TheReincarnator/leguino/docs/ideas/Robotik-für-Kinder.jpg

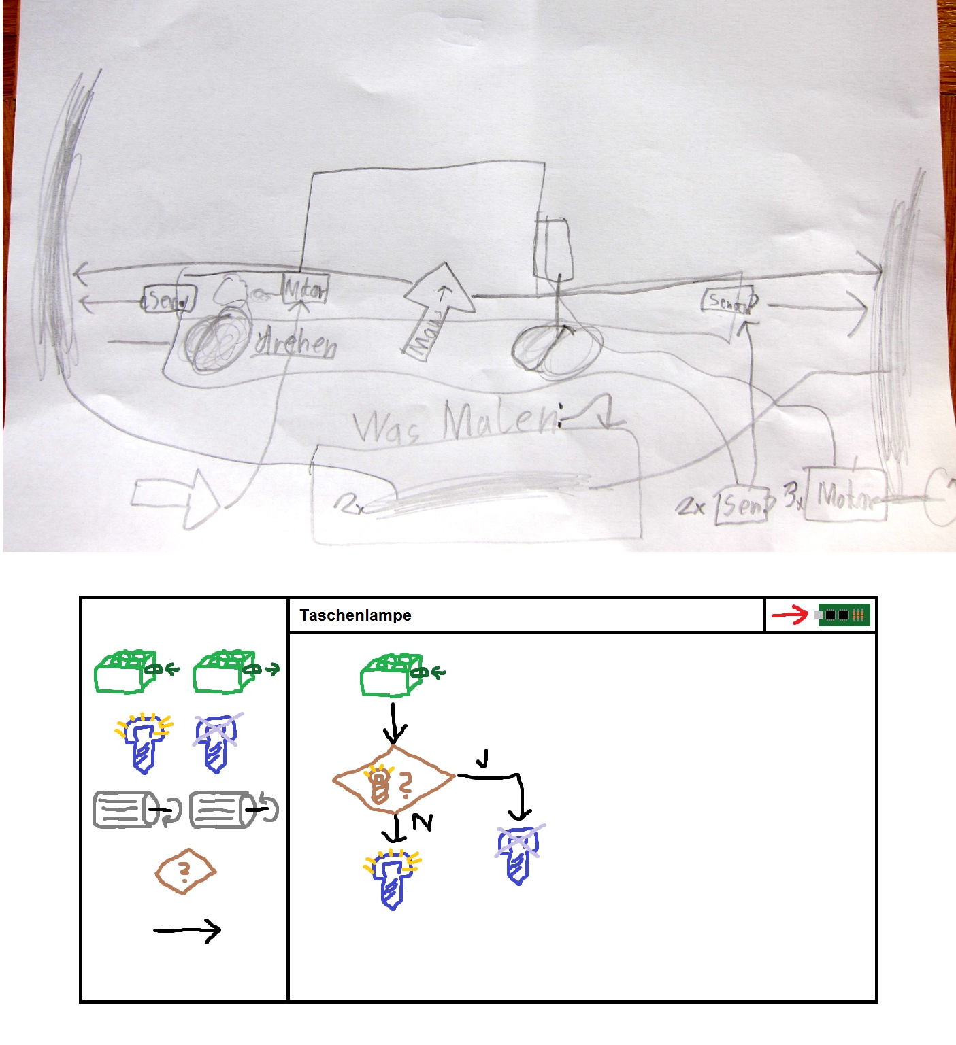
docs/ideas/Robotik-für-Kinder.jpg
