TheReincarnator/leguino/docs/photos/Leguino-Hardware-1.jpg

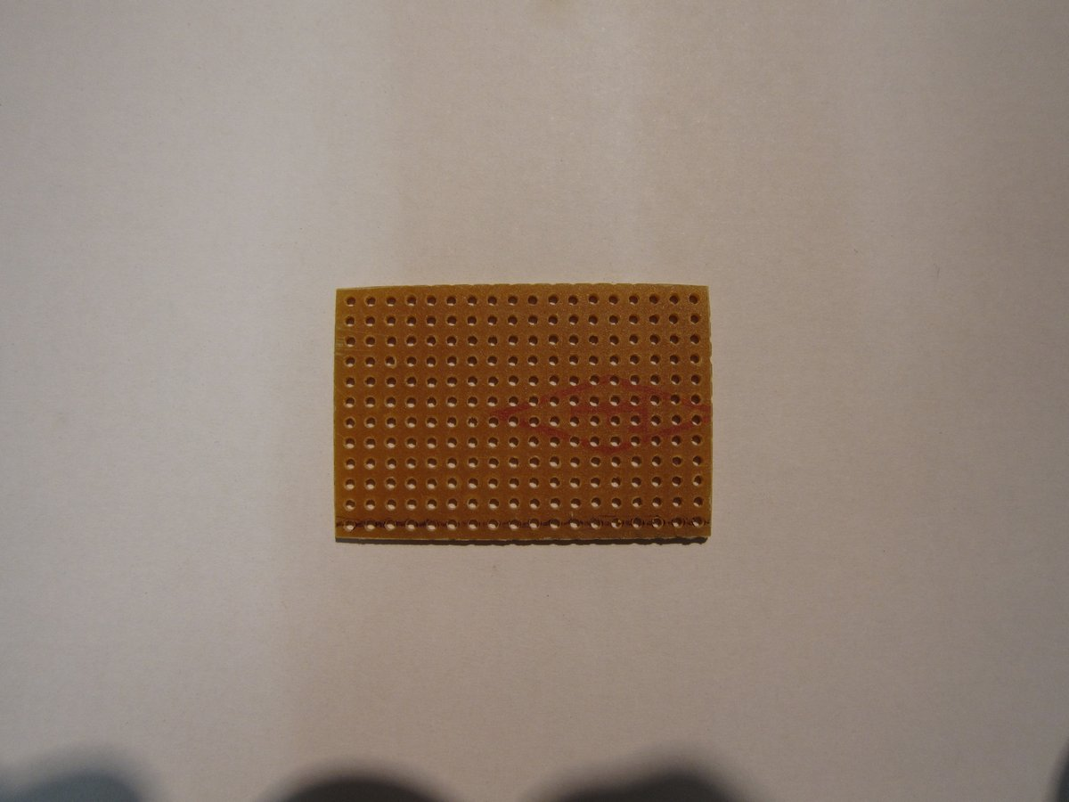
docs/photos/Leguino-Hardware-1.jpg
