TheReincarnator/leguino/docs/photos/Leguino-Hardware-3.jpg

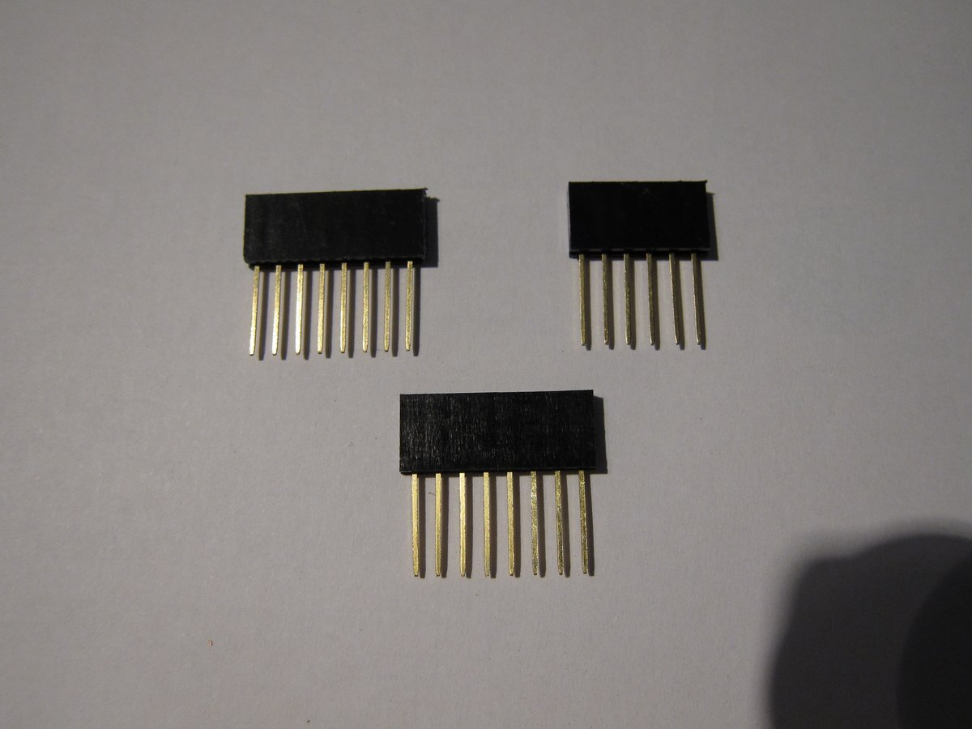
docs/photos/Leguino-Hardware-3.jpg
