TheReincarnator/leguino/docs/photos/Leguino-Hardware-4.jpg

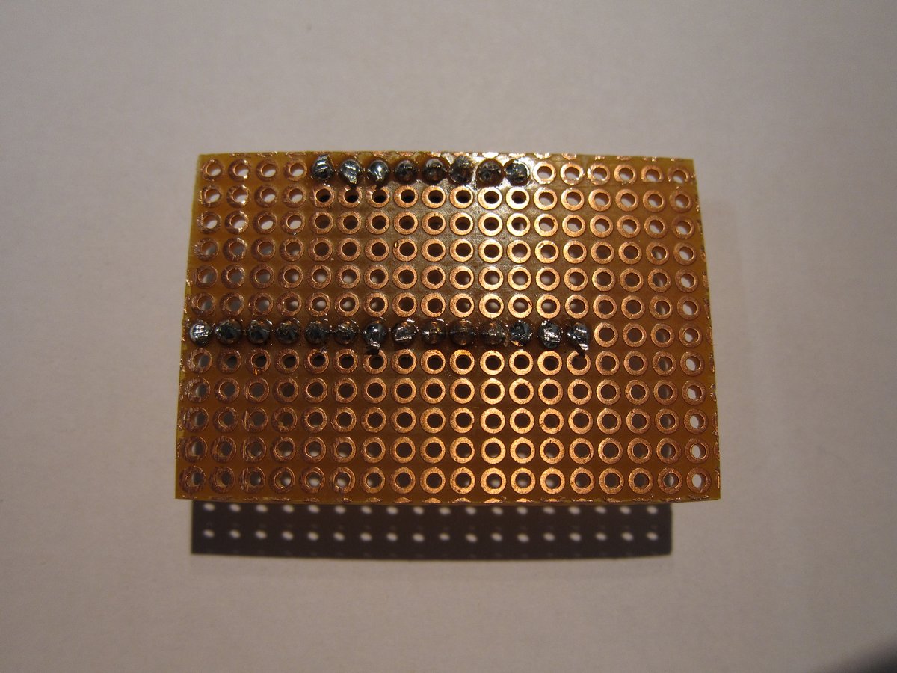
docs/photos/Leguino-Hardware-4.jpg
