TheReincarnator/leguino/docs/photos/Leguino-Hardware-5.jpg

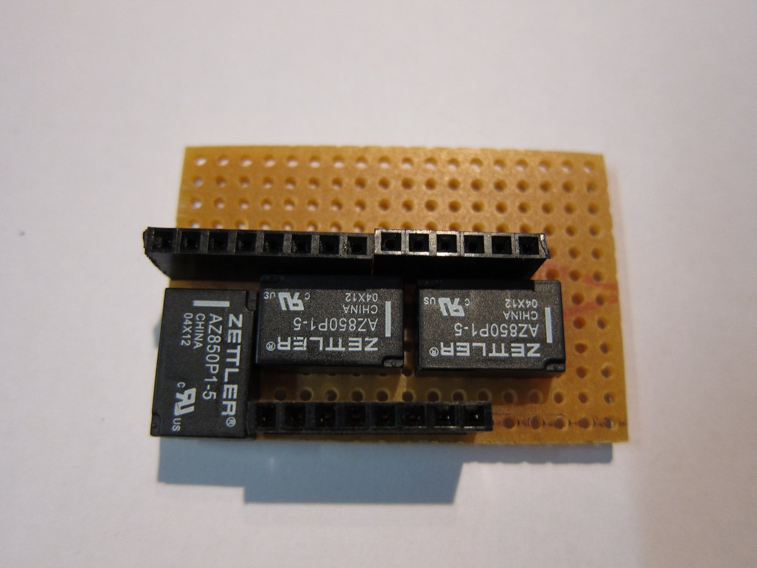
docs/photos/Leguino-Hardware-5.jpg
