TheReincarnator/leguino/docs/photos/Leguino-Hardware-6.jpg

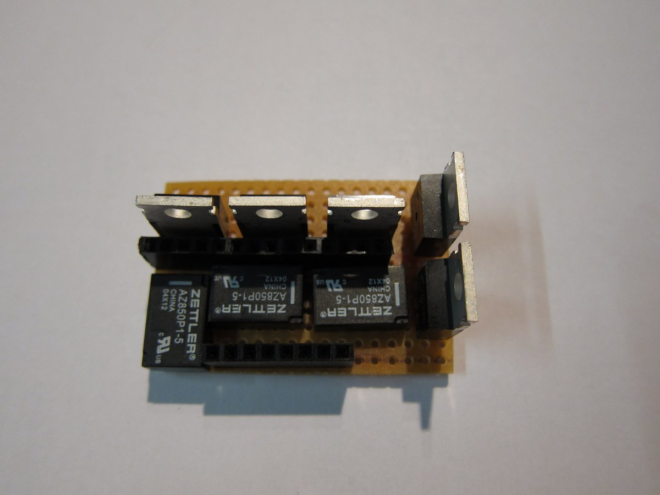
docs/photos/Leguino-Hardware-6.jpg
