TheReincarnator/leguino/docs/photos/Leguino-Hardware-7.jpg

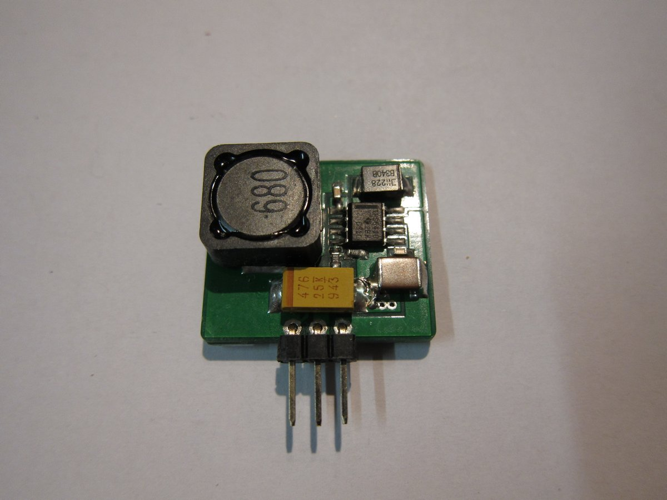
docs/photos/Leguino-Hardware-7.jpg
