TheReincarnator/leguino/docs/photos/Leguino-Hardware-8.jpg

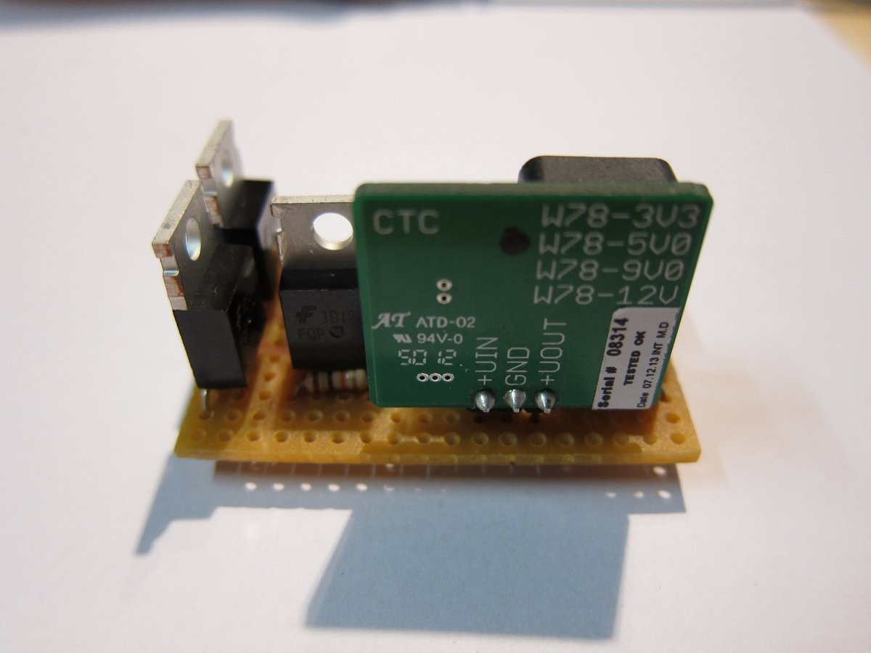
docs/photos/Leguino-Hardware-8.jpg
