TheReincarnator/leguino/docs/photos/Leguino-Hardware-9.jpg

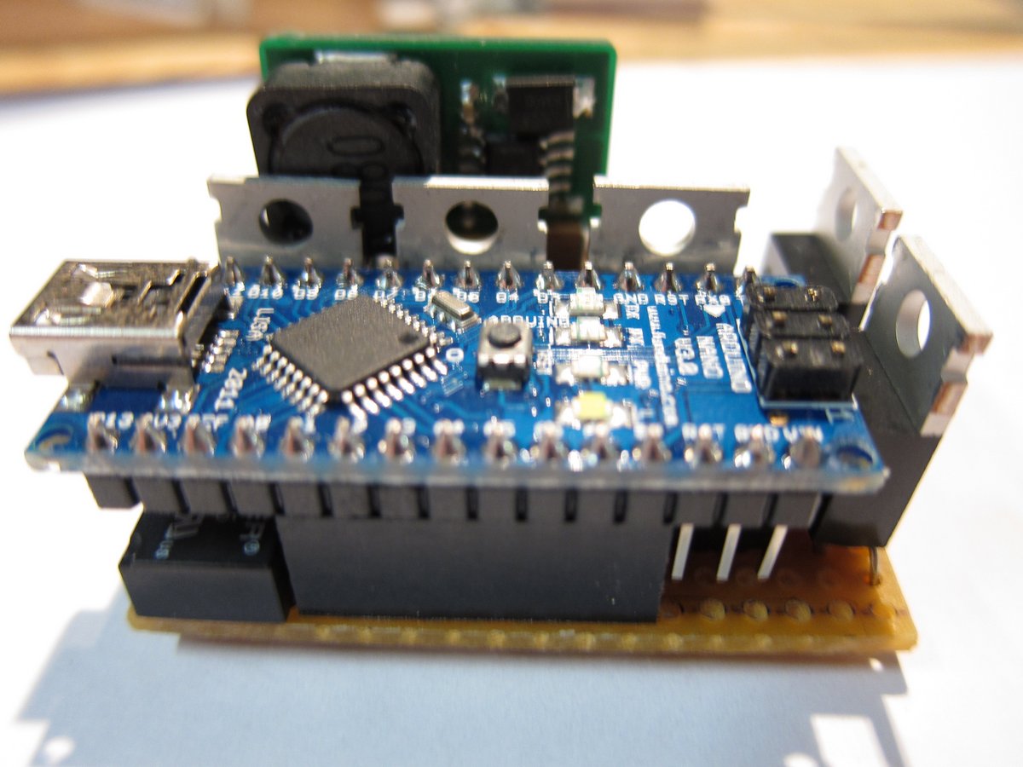
docs/photos/Leguino-Hardware-9.jpg
