TheReincarnator/leguino/docs/photos/Leguino-Hardware-10.jpg

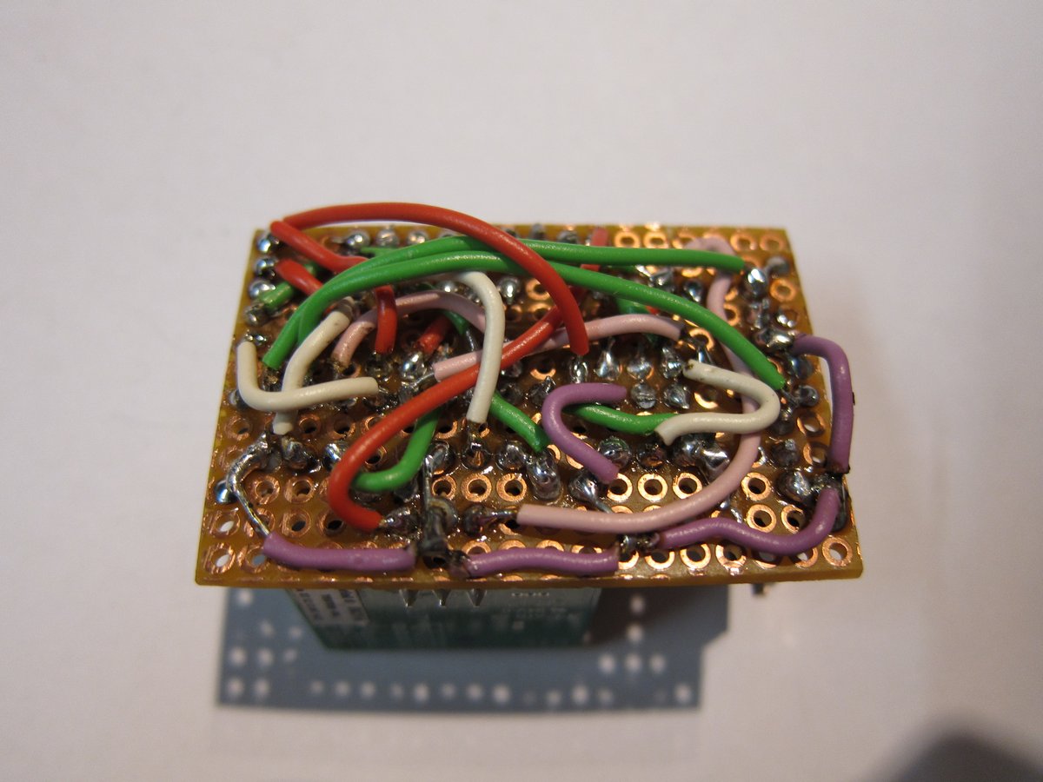
docs/photos/Leguino-Hardware-10.jpg
