TheReincarnator/leguino/docs/photos/Leguino-Hardware-12.jpg

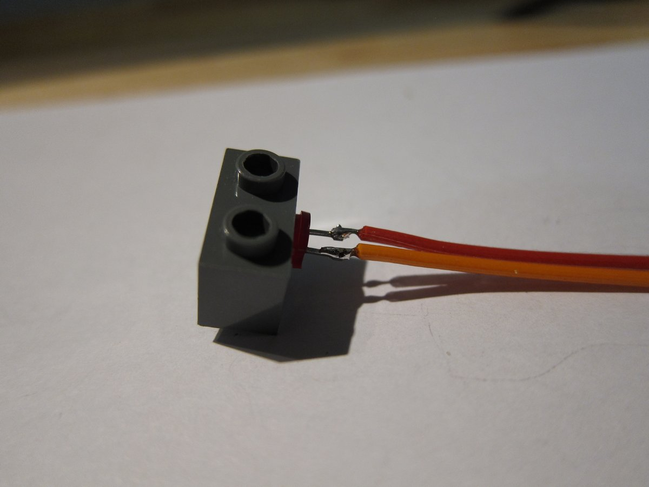
docs/photos/Leguino-Hardware-12.jpg
