TheReincarnator/leguino/docs/photos/Leguino-Hardware-13.jpg

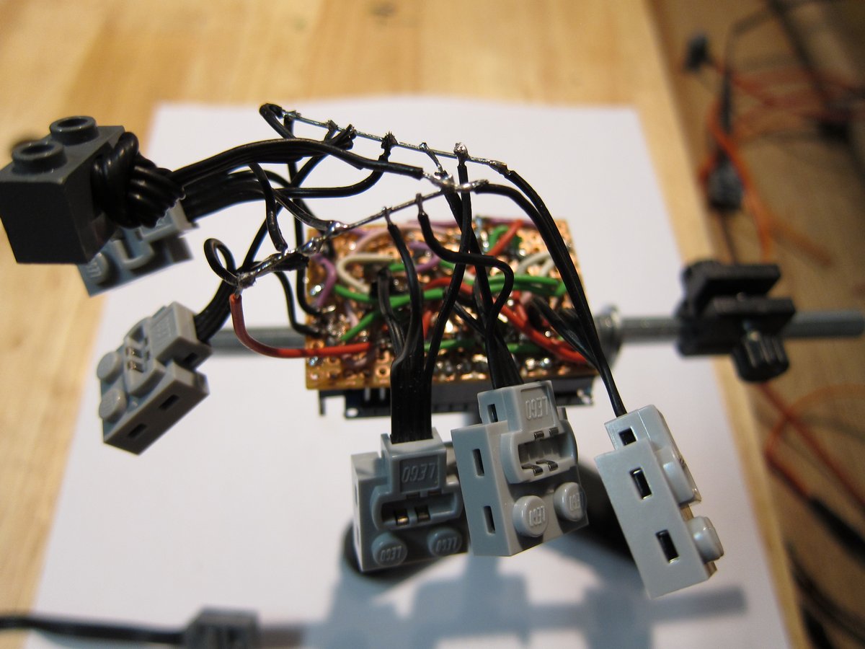
docs/photos/Leguino-Hardware-13.jpg
