TheReincarnator/leguino/docs/photos/Leguino-Hardware-14.jpg

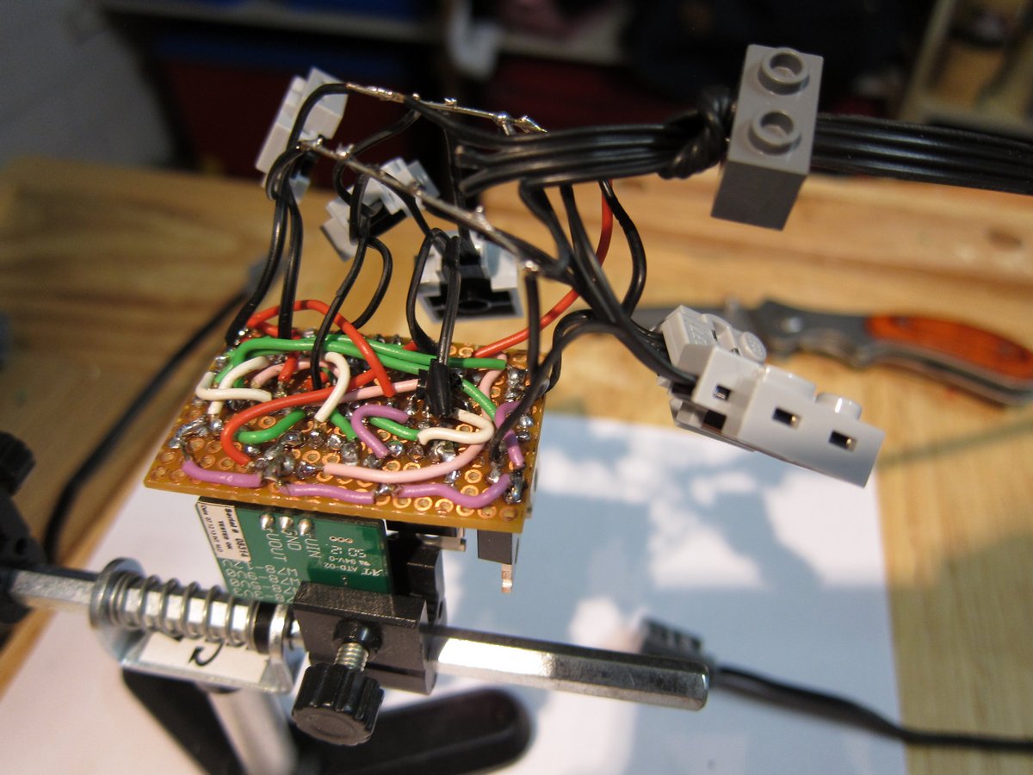
docs/photos/Leguino-Hardware-14.jpg
