TheReincarnator/leguino/docs/photos/Leguino-Hardware-17.jpg

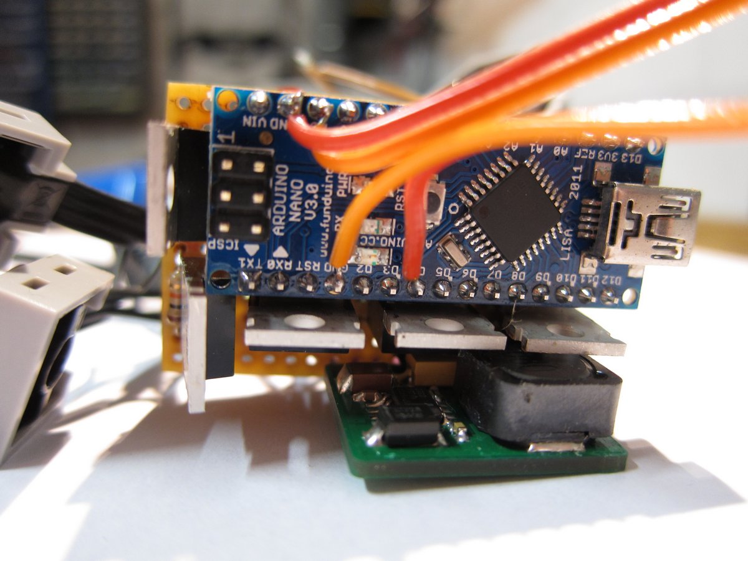
docs/photos/Leguino-Hardware-17.jpg
