TheReincarnator/leguino/docs/photos/Leguino-Hardware-18.jpg

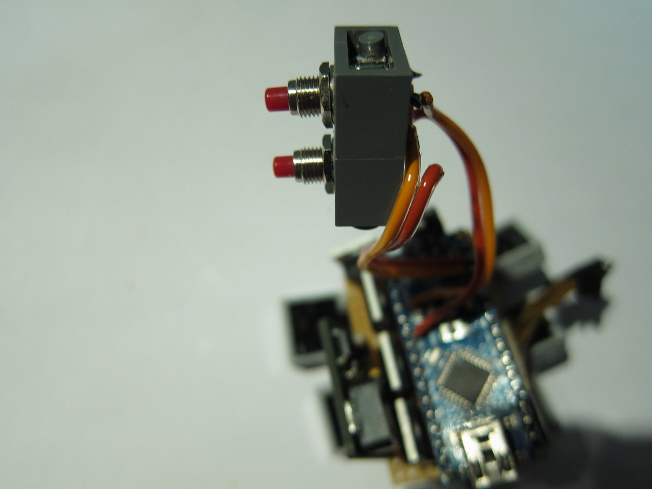
docs/photos/Leguino-Hardware-18.jpg
