TheReincarnator/leguino/docs/photos/Leguino-Hardware-19.jpg

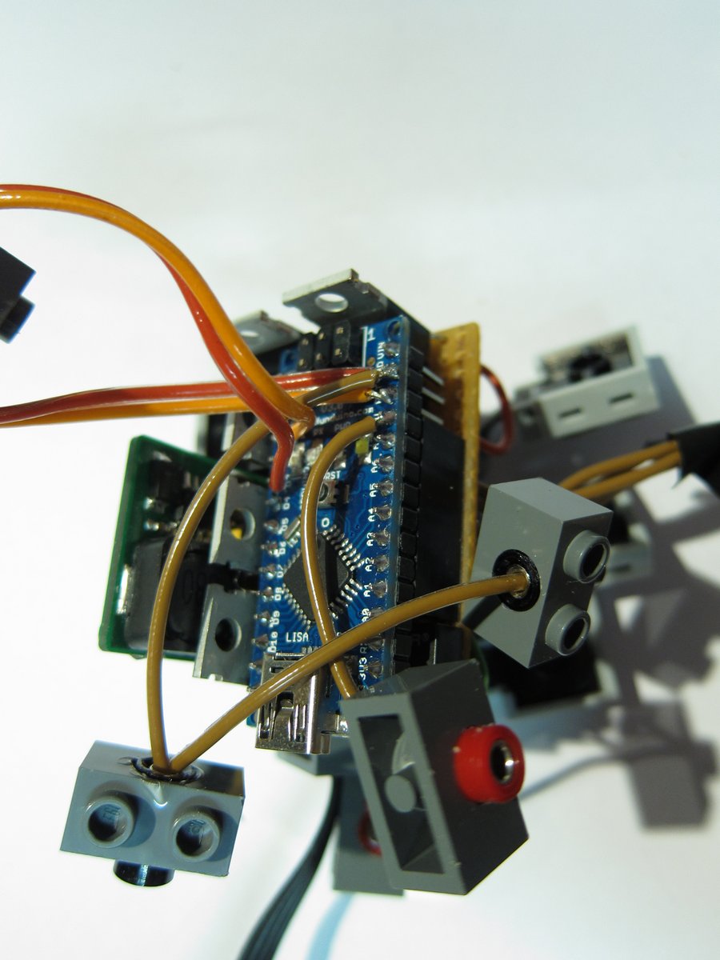
docs/photos/Leguino-Hardware-19.jpg
