TheReincarnator/leguino/docs/photos/Leguino-Hardware-22.jpg

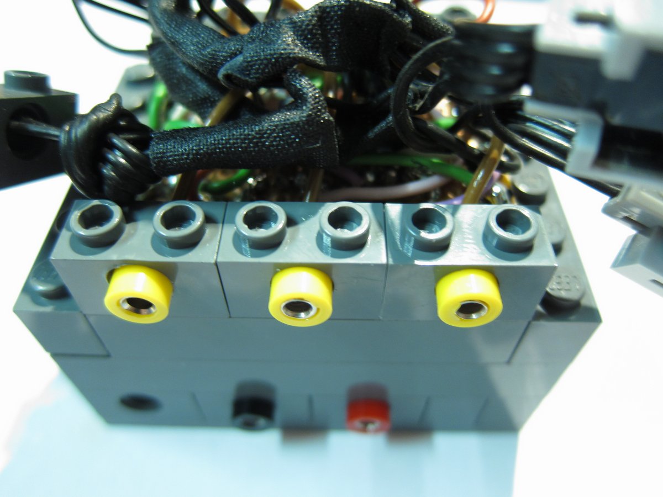
docs/photos/Leguino-Hardware-22.jpg
