TheReincarnator/leguino/docs/photos/Leguino-Hardware-23.jpg

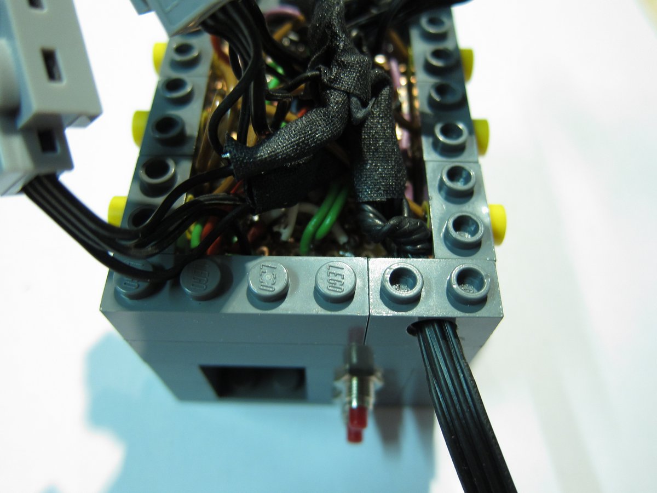
docs/photos/Leguino-Hardware-23.jpg
