TheReincarnator/leguino/docs/photos/Leguino-Hardware-24.jpg

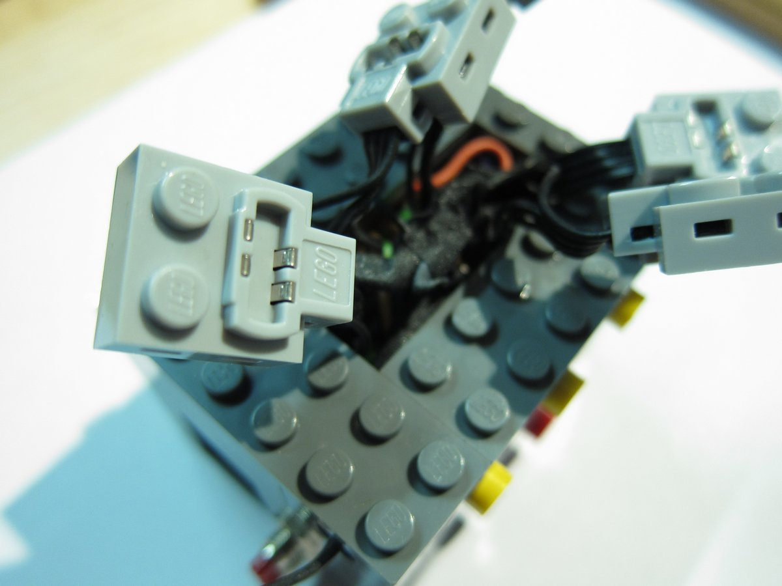
docs/photos/Leguino-Hardware-24.jpg
