TheReincarnator/leguino/docs/photos/Leguino-Hardware-25.jpg

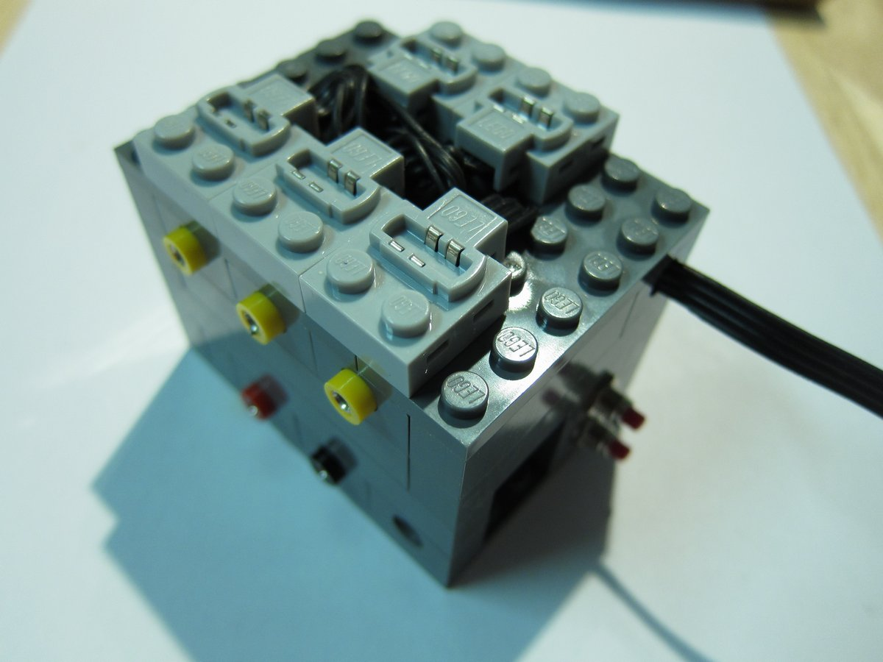
docs/photos/Leguino-Hardware-25.jpg
