TheReincarnator/leguino/docs/photos/Leguino-Hardware-26.jpg

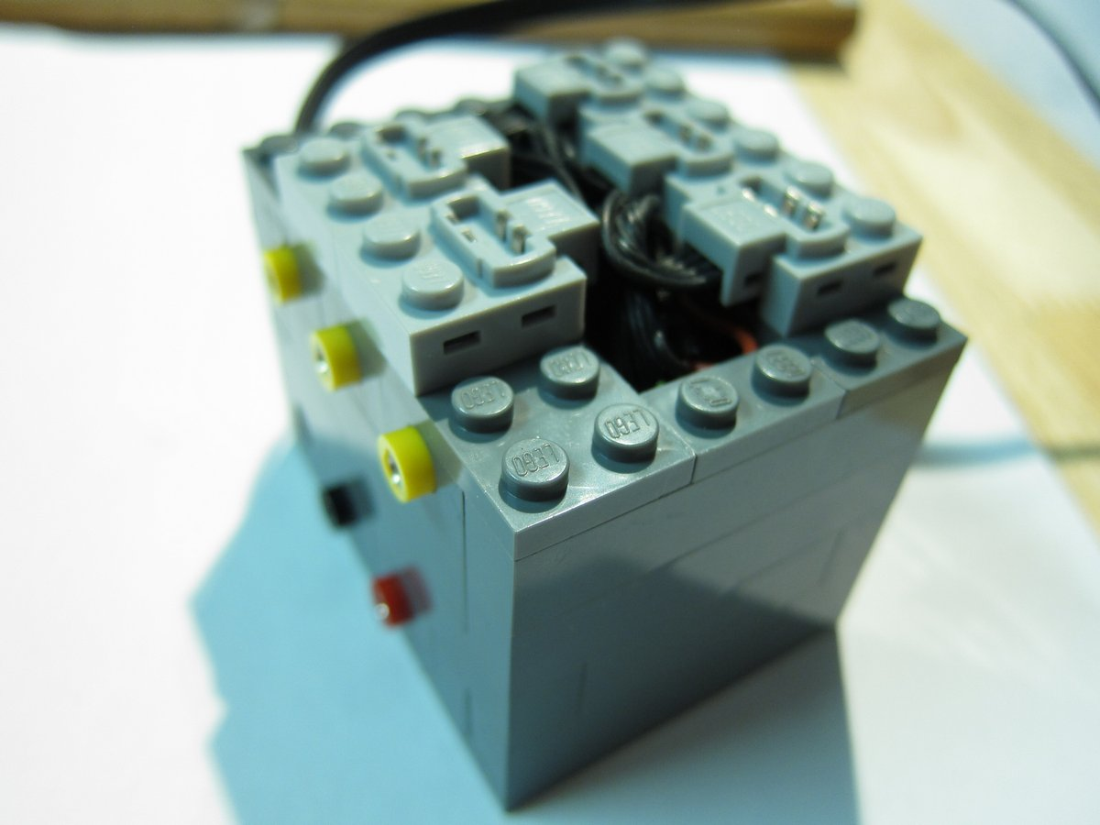
docs/photos/Leguino-Hardware-26.jpg
