TheReincarnator/leguino/docs/photos/Leguino-Hardware-27.jpg

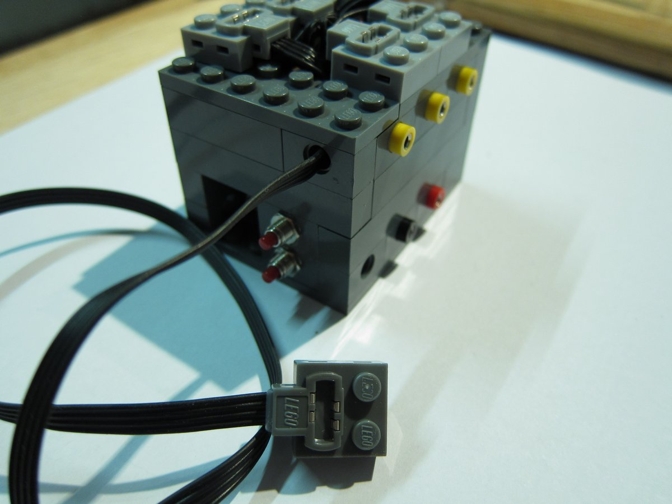
docs/photos/Leguino-Hardware-27.jpg
