TheReincarnator/leguino/docs/Power-Functions-assignment.jpg

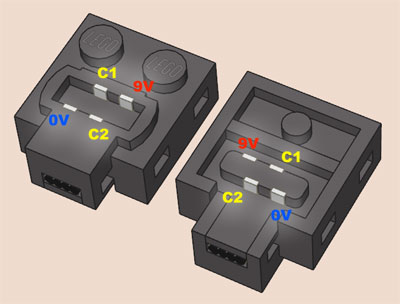
docs/Power-Functions-assignment.jpg
