TheReincarnator/leguino/docs/TQ2L25-bistable-relay-assignment.png

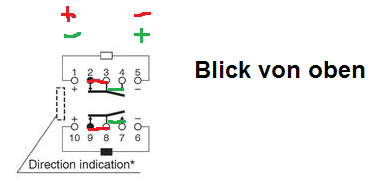
docs/TQ2L25-bistable-relay-assignment.png
