TheReincarnator/leguino/core/LeguinoTypes.h

#ifndef __LIGHT_TYPES_H
#define __LIGHT_TYPES_H


typedef signed char int8;
typedef unsigned char uint8;
typedef signed short int int16;
typedef unsigned short int uint16;
typedef signed long int int32;
typedef unsigned long int uint32;

#define NULL 0


#endif
